dirkandterra/ESP32_Dashboard/Software/GandL_esp32/EE.h

//EE.h
//-_-_-_-_-_-_-_-_-_-_-_-_-_-_-_-_-_-_-_-_-_-_-_-_-_-_-_-_
//Non-Volatile mem
//-_-_-_-_-_-_-_-_-_-_-_-_-_-_-_-_-_-_-_-_-_-_-_-_-_-_-_-_

#ifndef __EE_H
#define __EE_H

#include <EEPROM.h>
#include "secret.h"
#include "CANDash.h"

enum{
  GMODE_SERIAL,
  GMODE_WEATHER,
  GMODE_TSTAT,
  GMODE_CAN,
  GMODE_END
};

typedef struct{
  uint8_t initialized;
  char ssid[50];
  char pwd[30];
  ChanConfig_t chanCfg[NUM_CHANNELS];
  uint8_t gaugeMode;
} EEVars;

extern uint8_t GaugeMode;
extern EEVars EE;
void init_EEVars(void);
void Save_GaugeMode(void);
void Save_CANChan(ChanConfig_t *cfg);

#endif
