dirkandterra/ESP32_Dashboard/Software/GandL_esp32/GandL.h

#ifndef GandL_h
#define GandL_h


	void sendInfo(uint8_t gauge, uint16_t value);
  void sendVFD(uint8_t *c);
	void testVFD(uint16_t value);
  extern void vfdWeatherPrep(void);
  extern void DecodeInit(void);
  void updateGuages_Lights(void);

#endif
